SP5GW/garden_lights_rb_pi_zero/hw/HW_Generation_2_0/IMG_0502.jpg

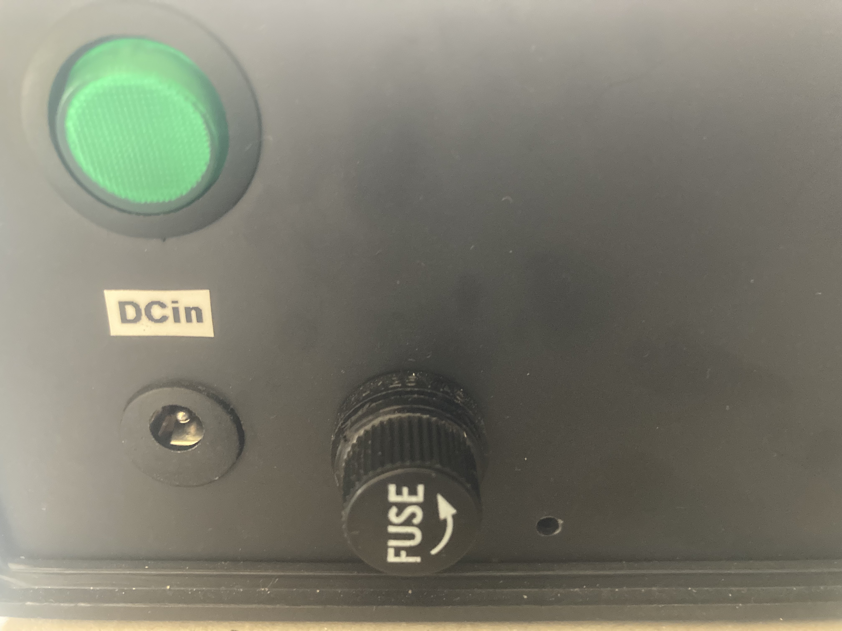
hw/HW_Generation_2_0/IMG_0502.jpg
