SP5GW/garden_lights_rb_pi_zero/hw/HW_Generation_5_0/IMG_0576.jpg

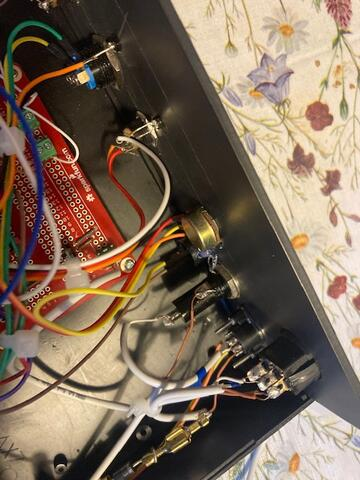
hw/HW_Generation_5_0/IMG_0576.jpg
