SP5GW/garden_lights_rb_pi_zero/hw/HW_Generation_5_0/IMG_0578.jpg

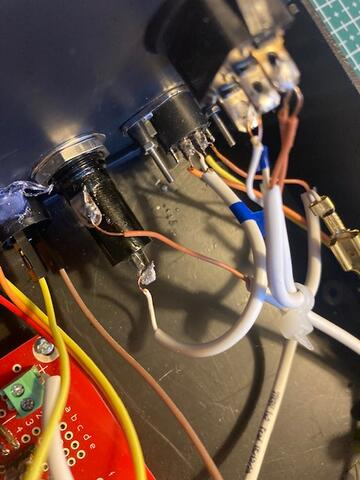
hw/HW_Generation_5_0/IMG_0578.jpg
