SP5GW/garden_lights_rb_pi_zero/hw/HW_Generation_1_0/IMG_0478.jpg

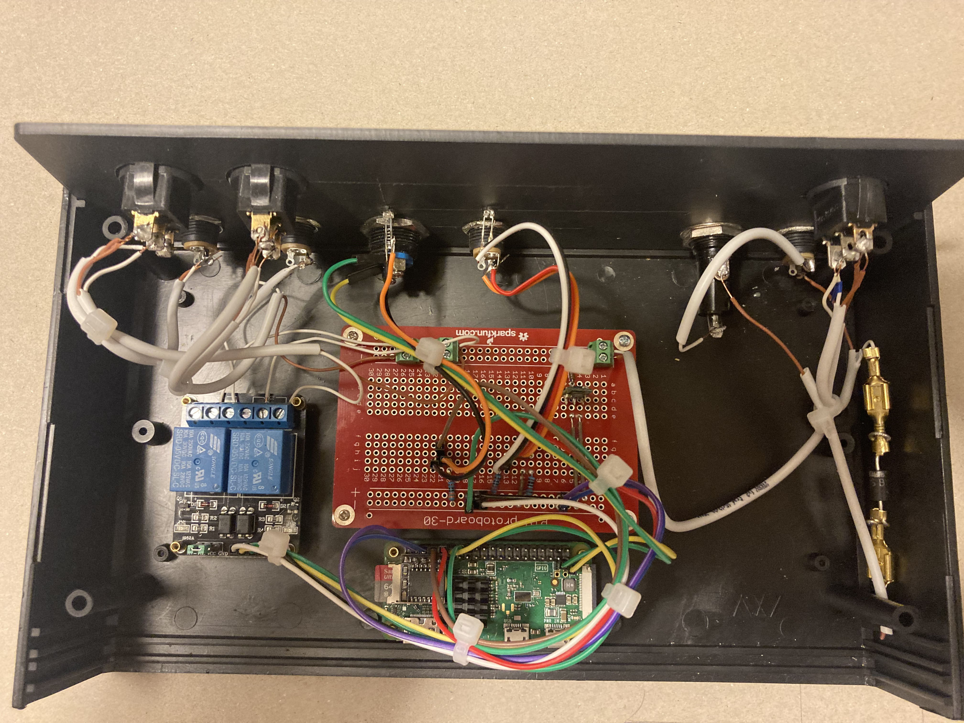
hw/HW_Generation_1_0/IMG_0478.jpg
