SP5GW/garden_lights_rb_pi_zero/hw/HW_Generation_4_0/IMG_0554.jpg

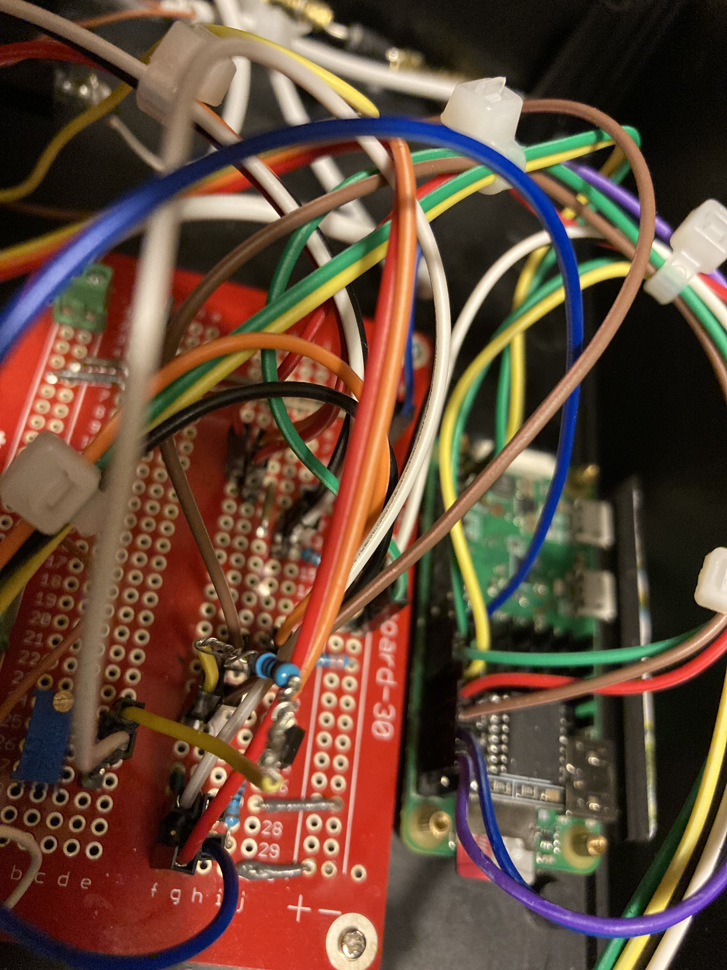
hw/HW_Generation_4_0/IMG_0554.jpg
